bencbartlett/3D-printed-mirror-array/img/IMG_0275.jpeg

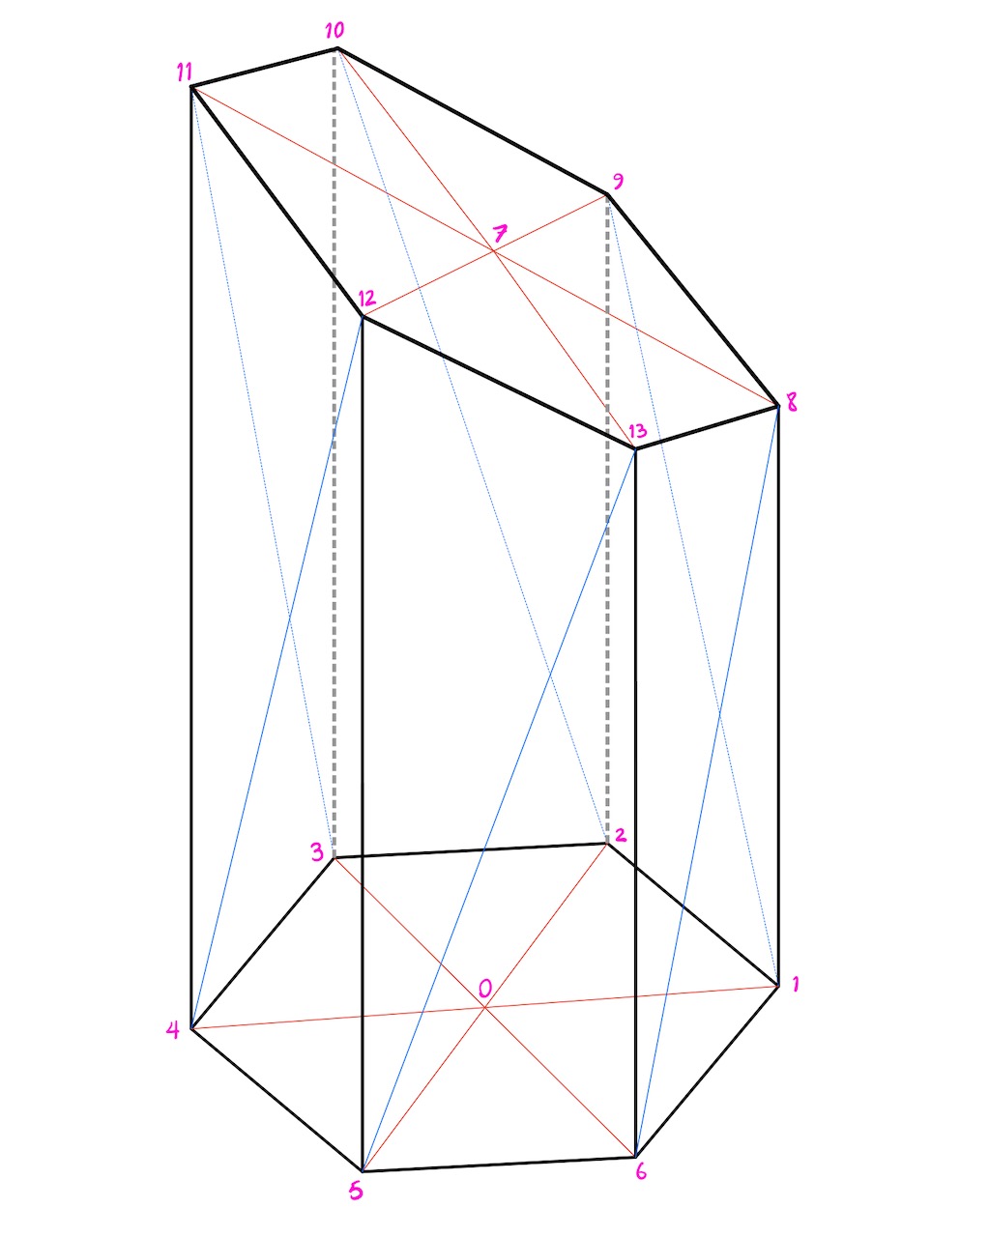
img/IMG_0275.jpeg
