bencbartlett/3D-printed-mirror-array/img/IMG_0276.jpeg

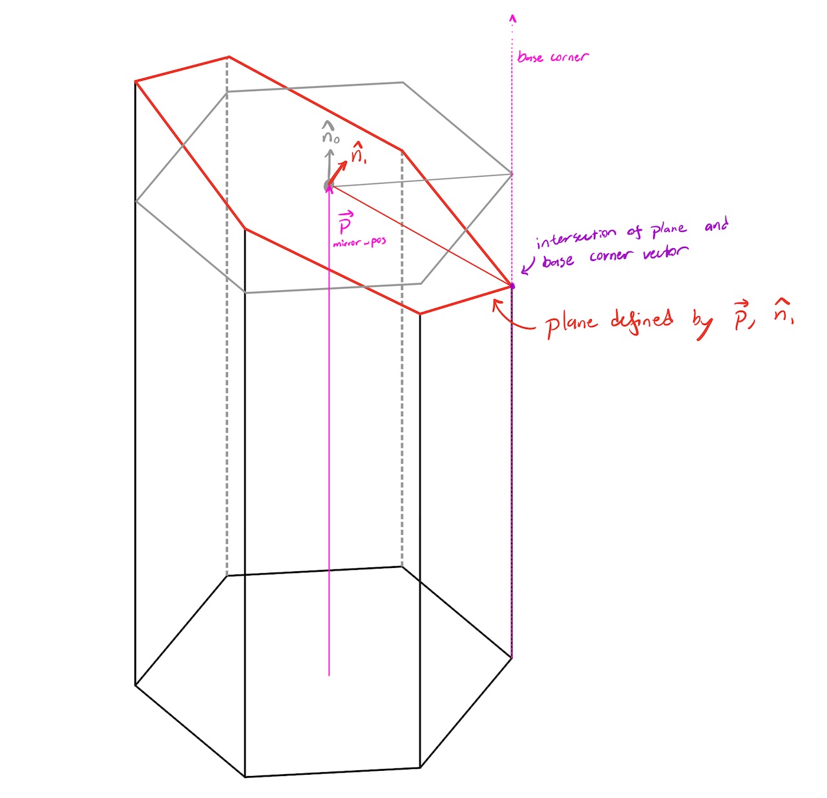
img/IMG_0276.jpeg
