bencbartlett/3D-printed-mirror-array/img/IMG_0277.jpeg

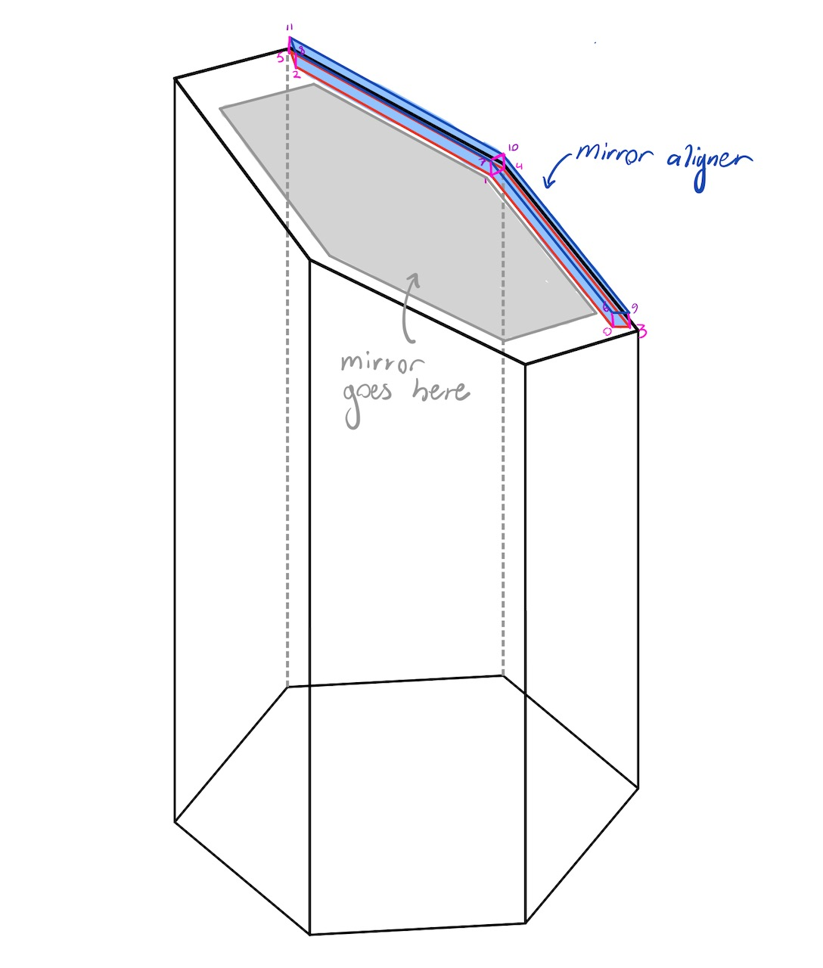
img/IMG_0277.jpeg
