bencbartlett/3D-printed-mirror-array/img/IMG_0278.jpeg

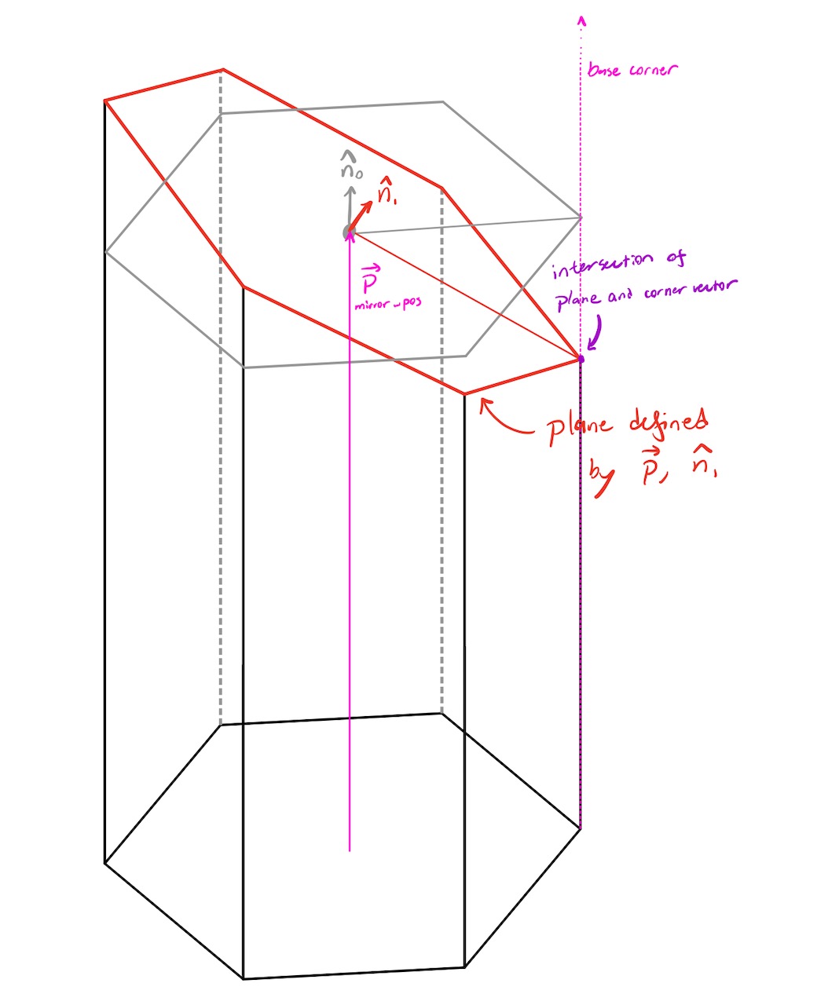
img/IMG_0278.jpeg
