bencbartlett/3D-printed-mirror-array/img/IMG_0745.jpeg

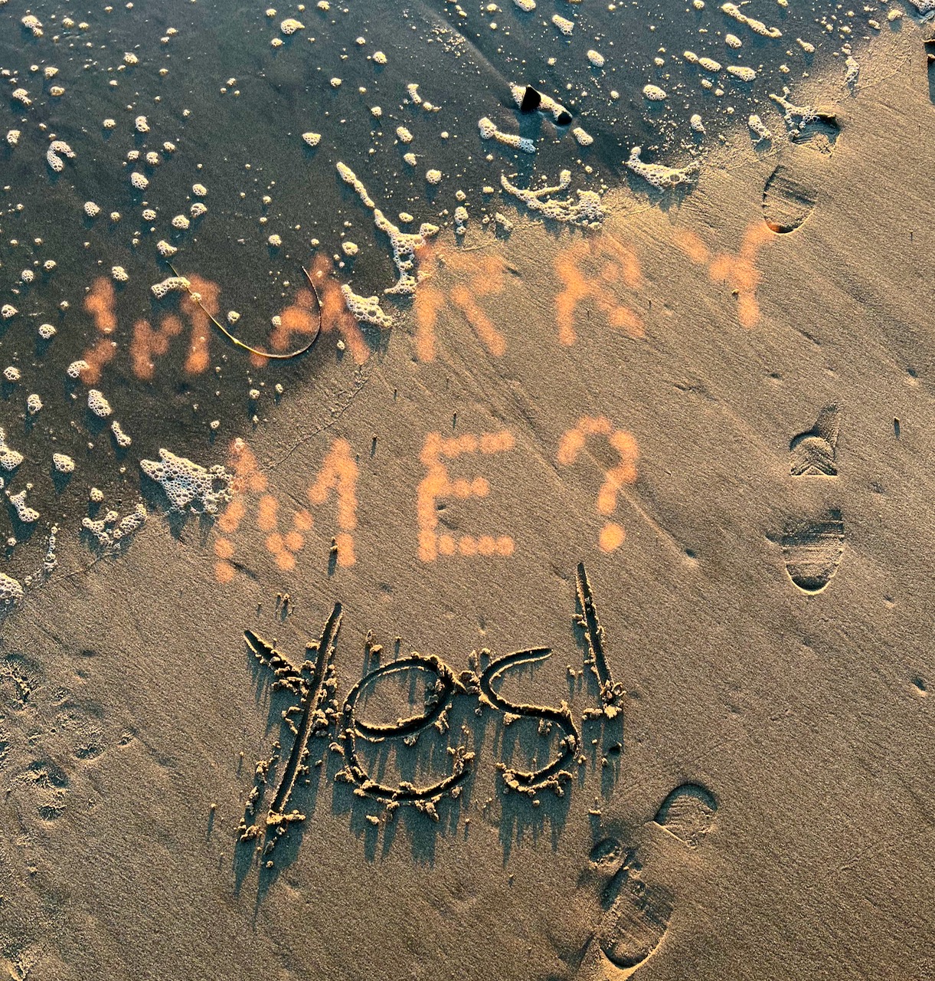
img/IMG_0745.jpeg
