bencbartlett/3D-printed-mirror-array/img/IMG_2569.jpeg

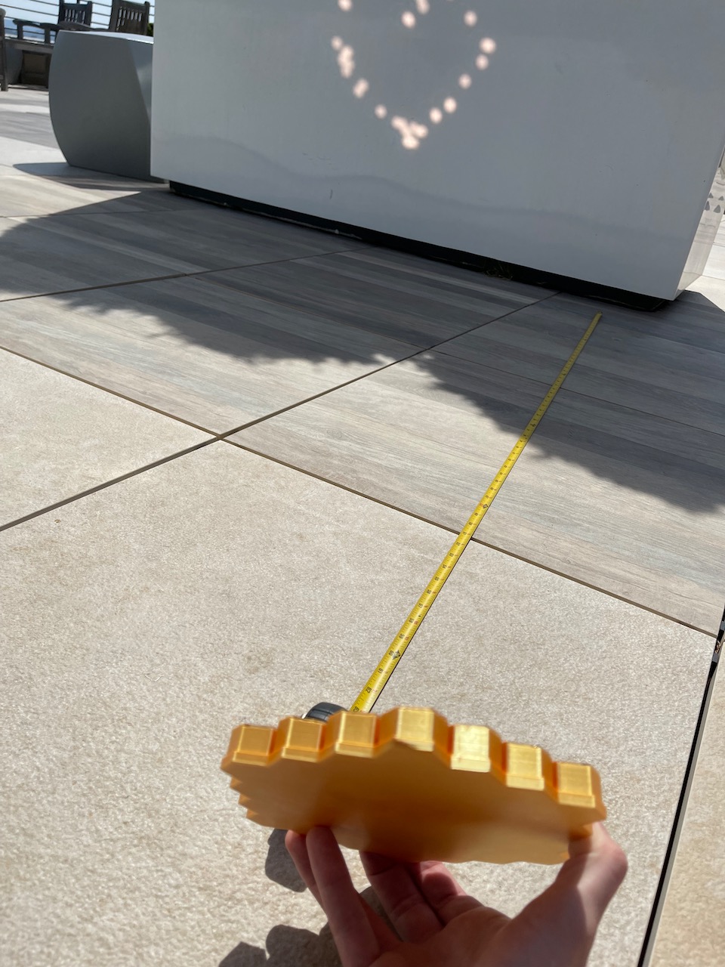
img/IMG_2569.jpeg
