bencbartlett/3D-printed-mirror-array/img/IMG_2590.jpeg

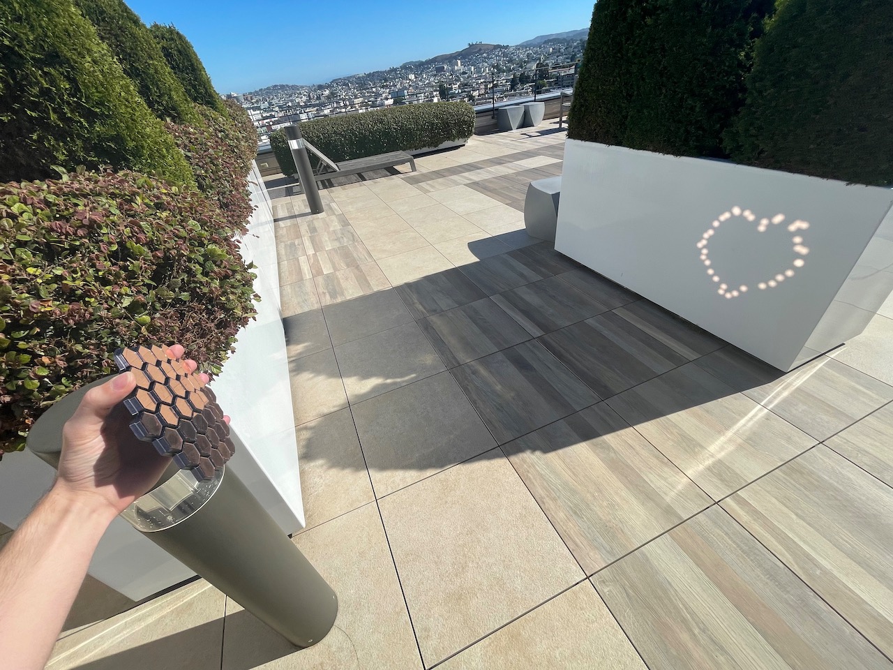
img/IMG_2590.jpeg
