bencbartlett/3D-printed-mirror-array/img/IMG_2880.jpeg

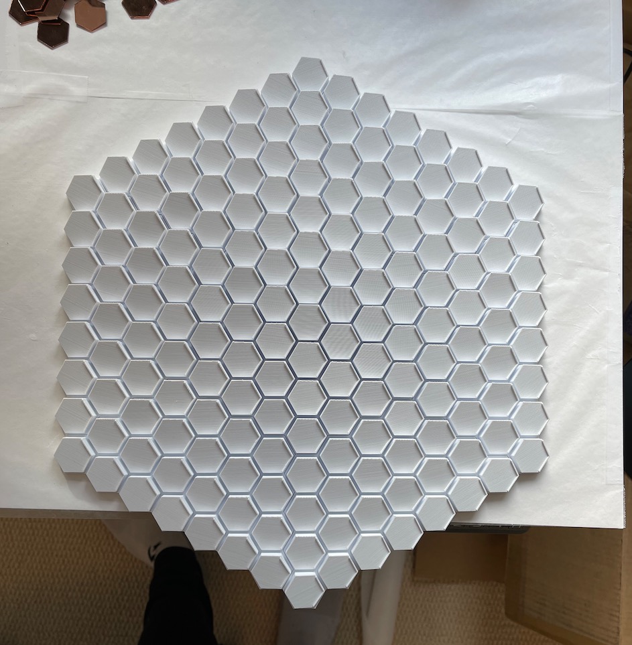
img/IMG_2880.jpeg
