bencbartlett/3D-printed-mirror-array/img/IMG_2881.jpeg

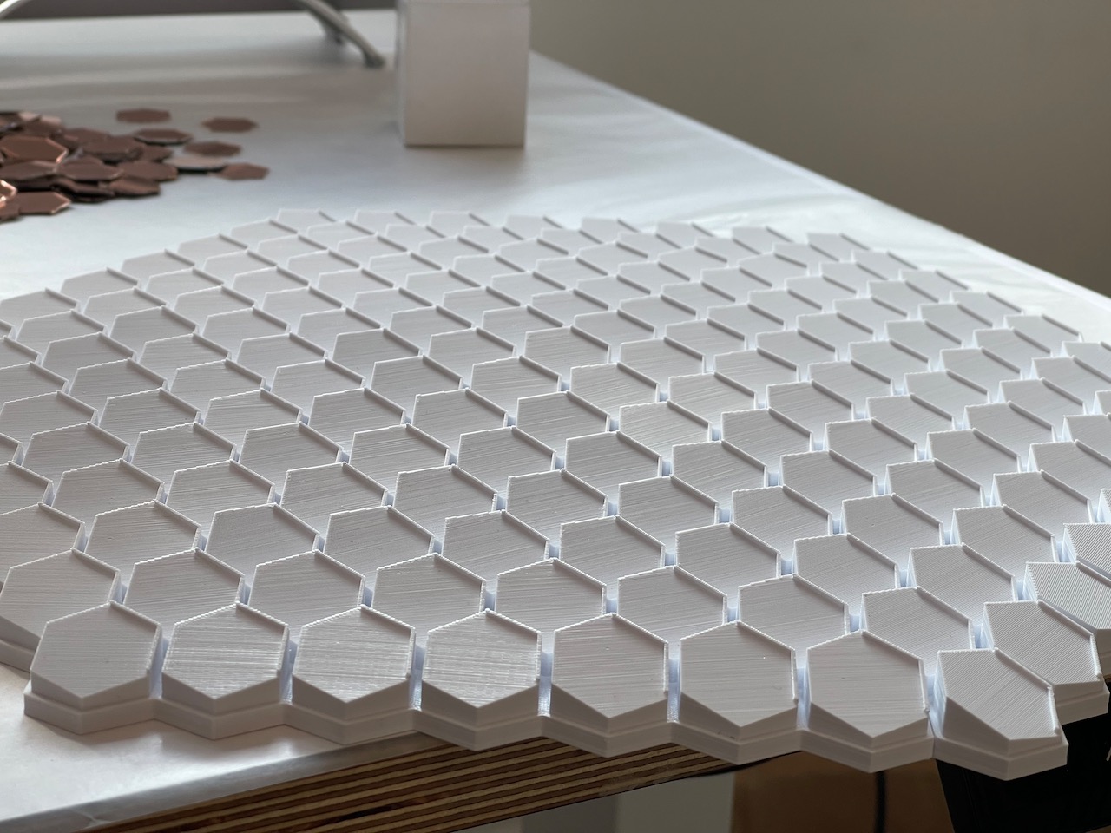
img/IMG_2881.jpeg
