bencbartlett/3D-printed-mirror-array/img/IMG_2882.jpeg

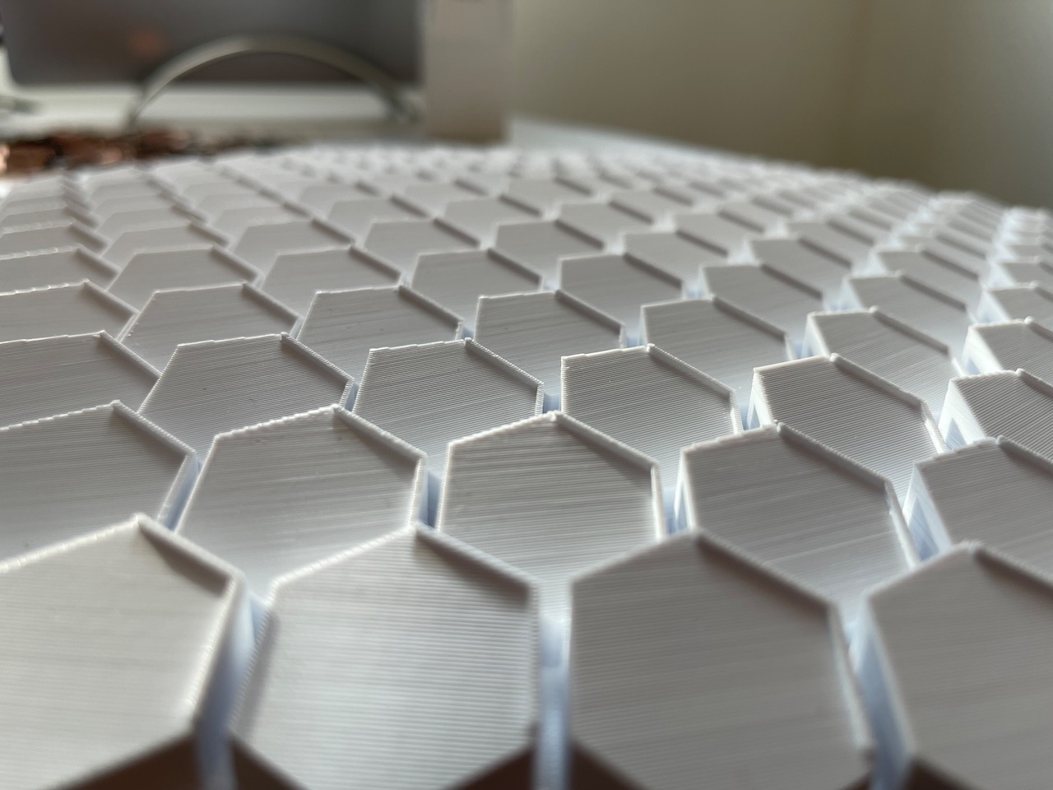
img/IMG_2882.jpeg
