bencbartlett/3D-printed-mirror-array/img/IMG_2884.jpeg

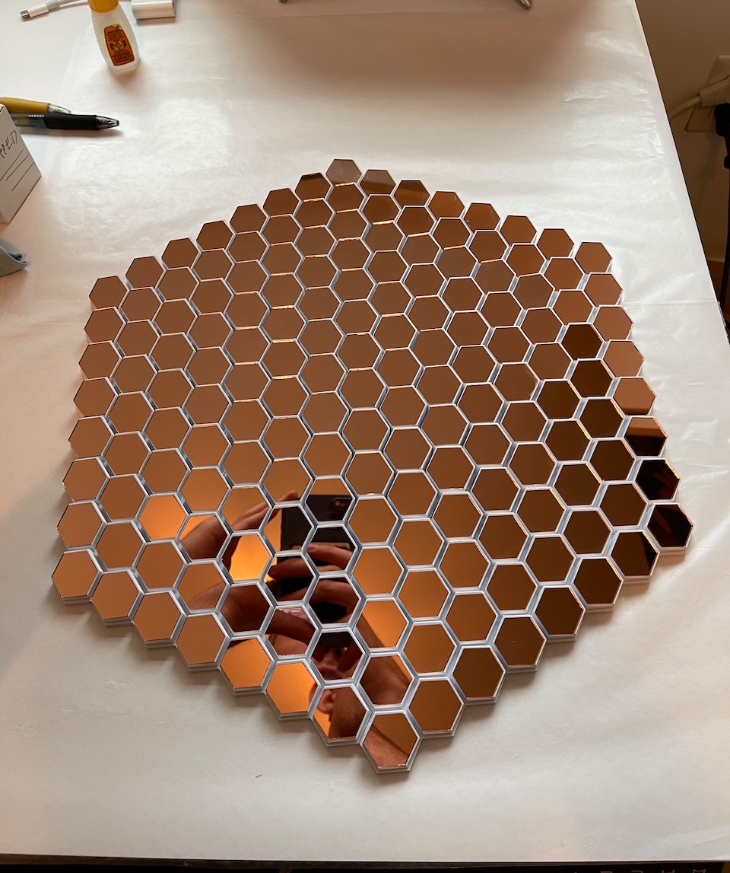
img/IMG_2884.jpeg
