bencbartlett/3D-printed-mirror-array/img/IMG_2885.jpeg

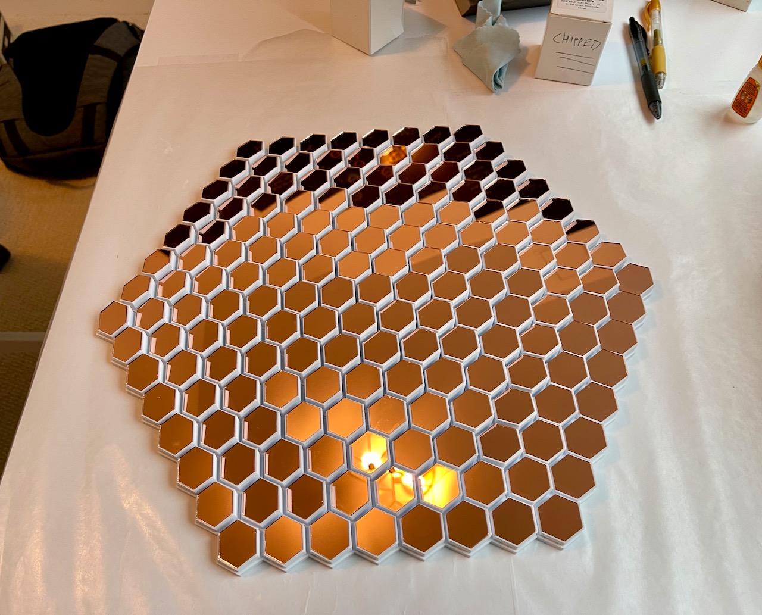
img/IMG_2885.jpeg
