bencbartlett/3D-printed-mirror-array/img/IMG_2955.jpeg

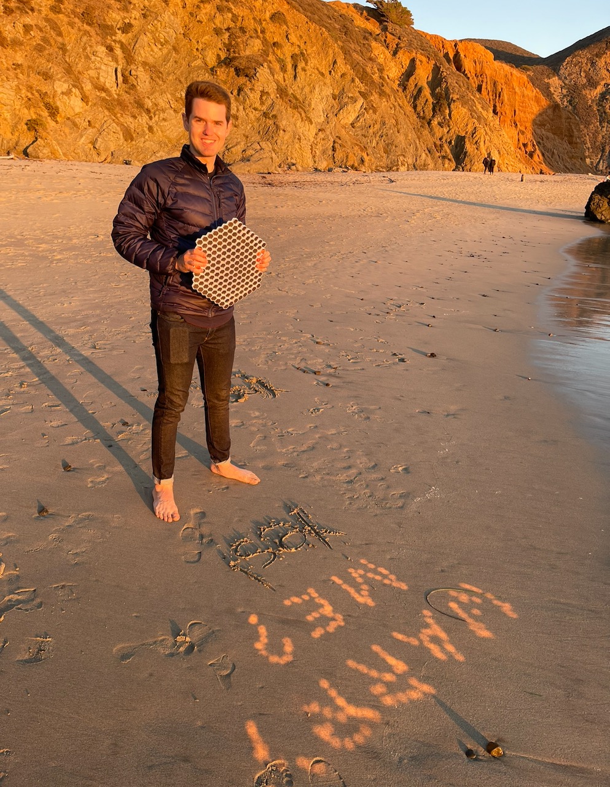
img/IMG_2955.jpeg
