bencbartlett/3D-printed-mirror-array/img/IMG_3002.jpeg

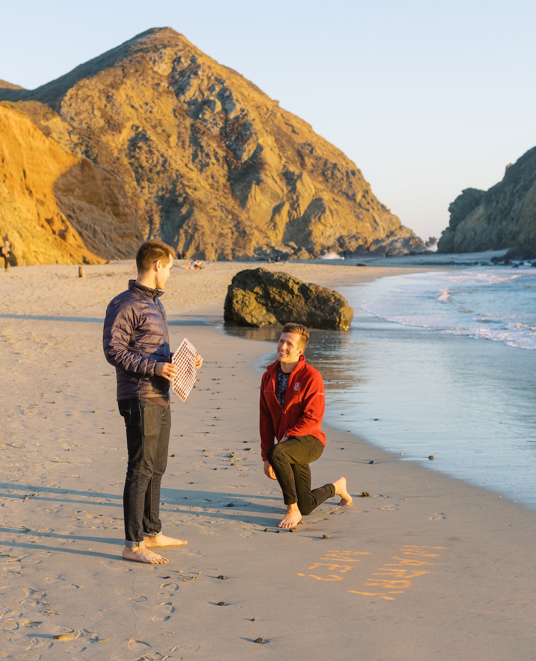
img/IMG_3002.jpeg
