bencbartlett/3D-printed-mirror-array/img/IMG_3013.jpeg

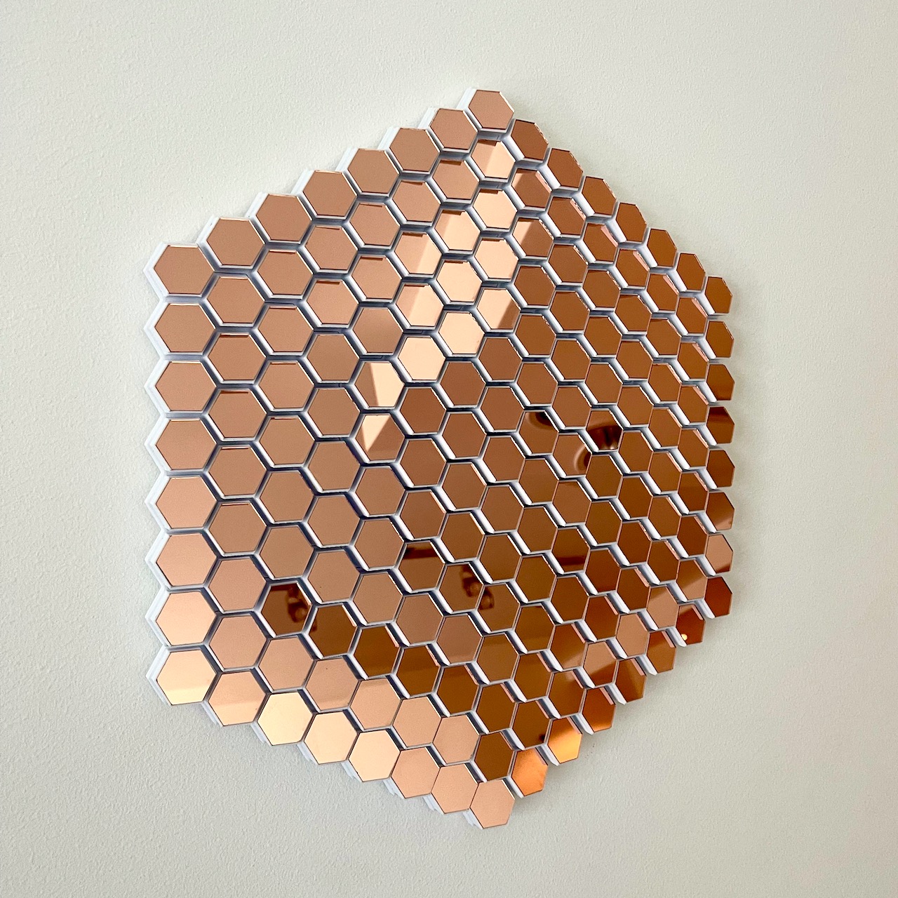
img/IMG_3013.jpeg
