bencbartlett/3D-printed-mirror-array/img/propose.jpeg

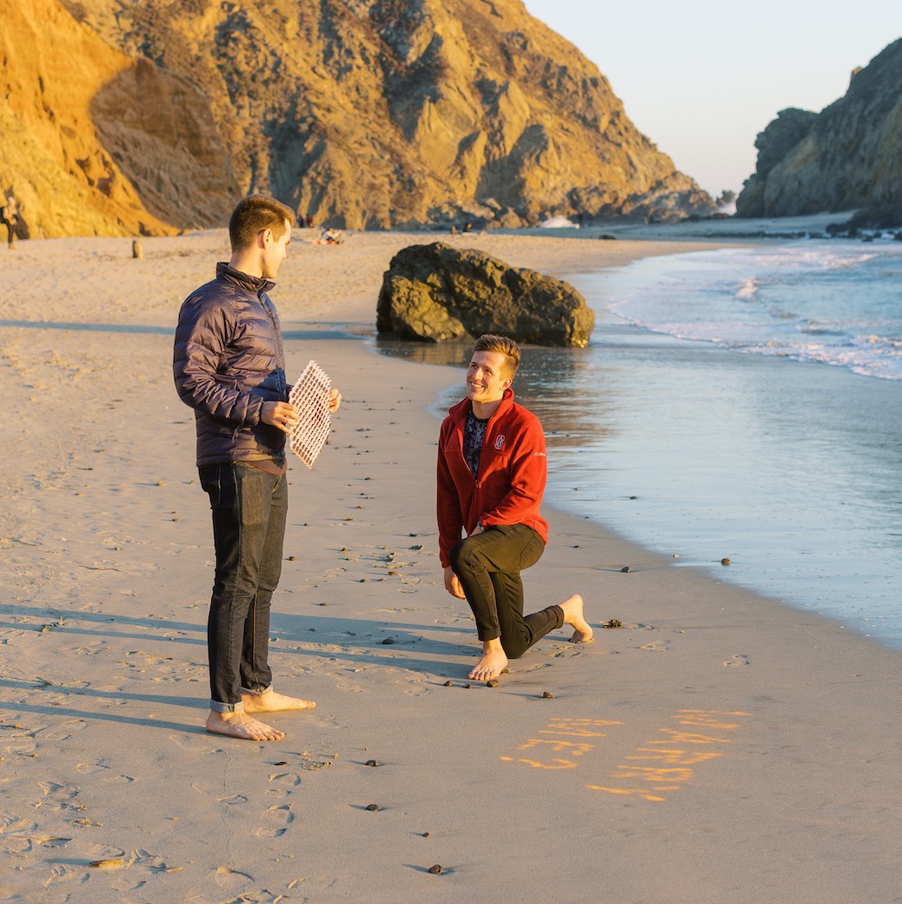
img/propose.jpeg
