bencbartlett/3D-printed-mirror-array/img/Screen Shot 2021-11-10 at 5.56.20 PM.jpeg

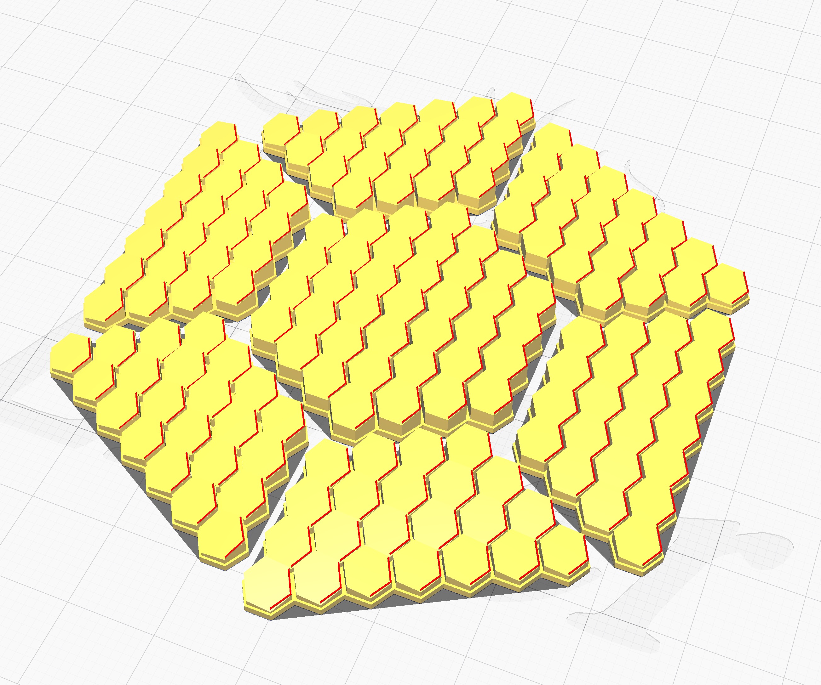
img/Screen Shot 2021-11-10 at 5.56.20 PM.jpeg
